CIRCUITSTATE/PBSEQ-D2/Export/R0.1/[1] 12-05-2024/PCB/PBSEQ-D2-R0.1-F_Paste.pdf

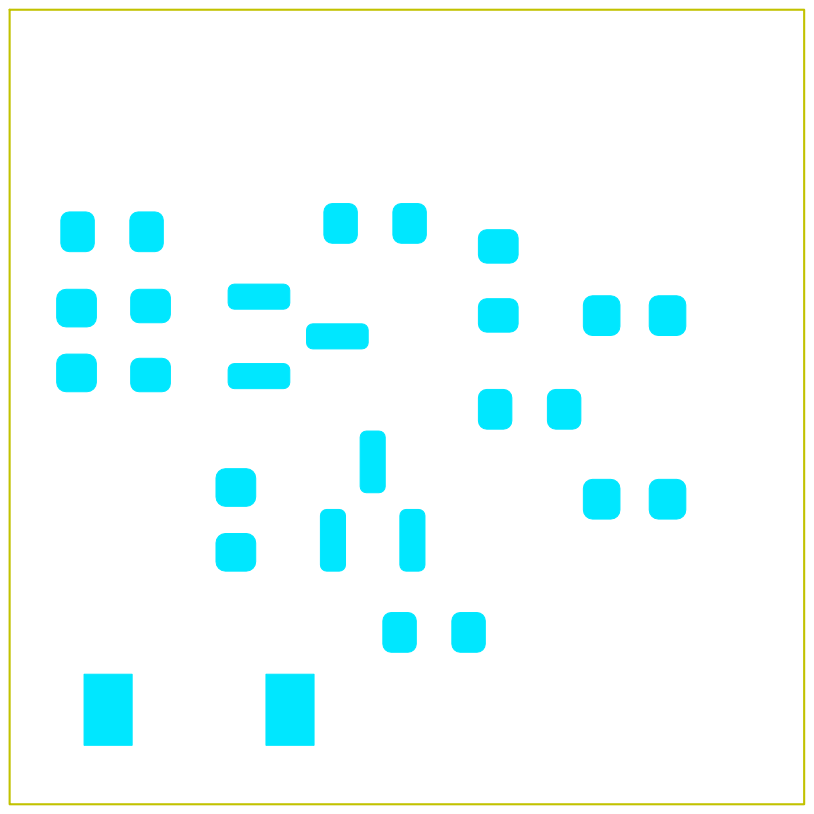
[picture p13: page 1]
