CIRCUITSTATE/PBSEQ-D2/Export/R0.1/[1] 12-05-2024/PCB/PBSEQ-D2-R0.1-F_Silkscreen.pdf

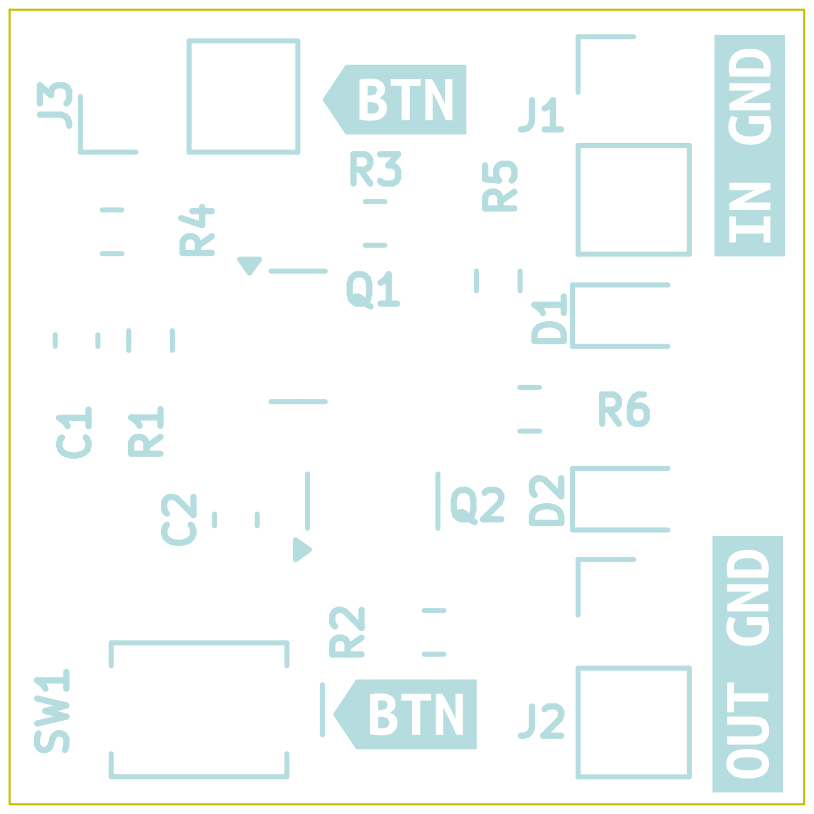
[picture p14: page 1]
