CIRCUITSTATE/PBSEQ-D2/Export/R0.1/[1] 12-05-2024/PCB/PBSEQ-D2-R0.1-User_Drawings.pdf

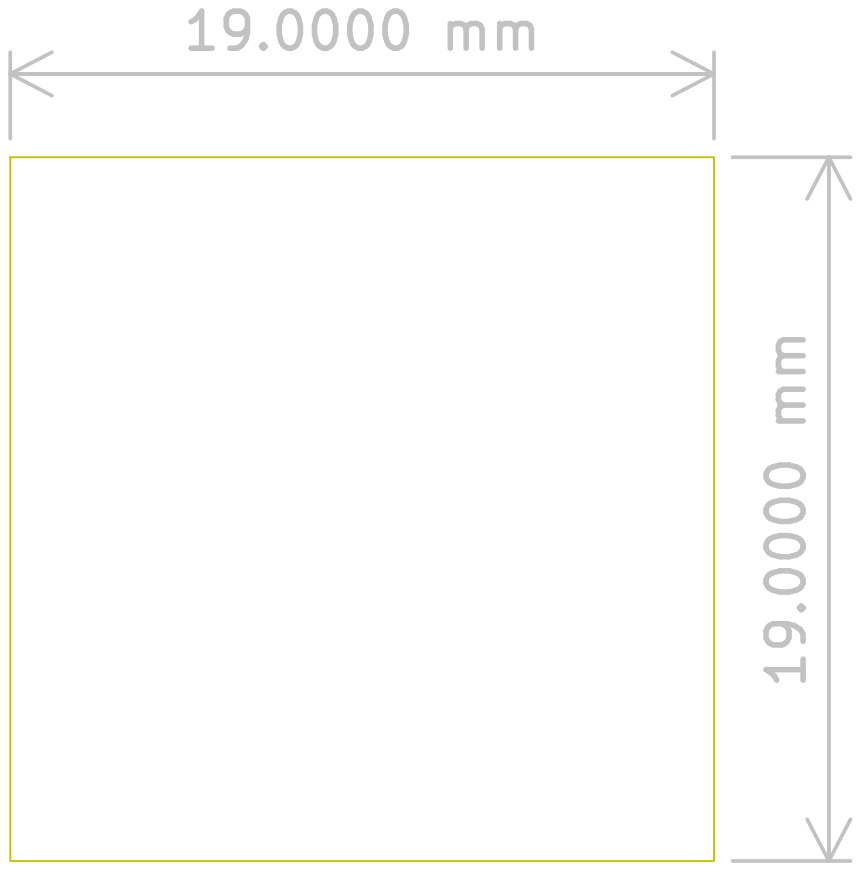
[picture p15: page 1]
