CIRCUITSTATE/PBSEQ-D2/Export/R0.1/[1] 12-05-2024/SCH/PBSEQ-D2-R0.1-SCH-12052024-1.pdf

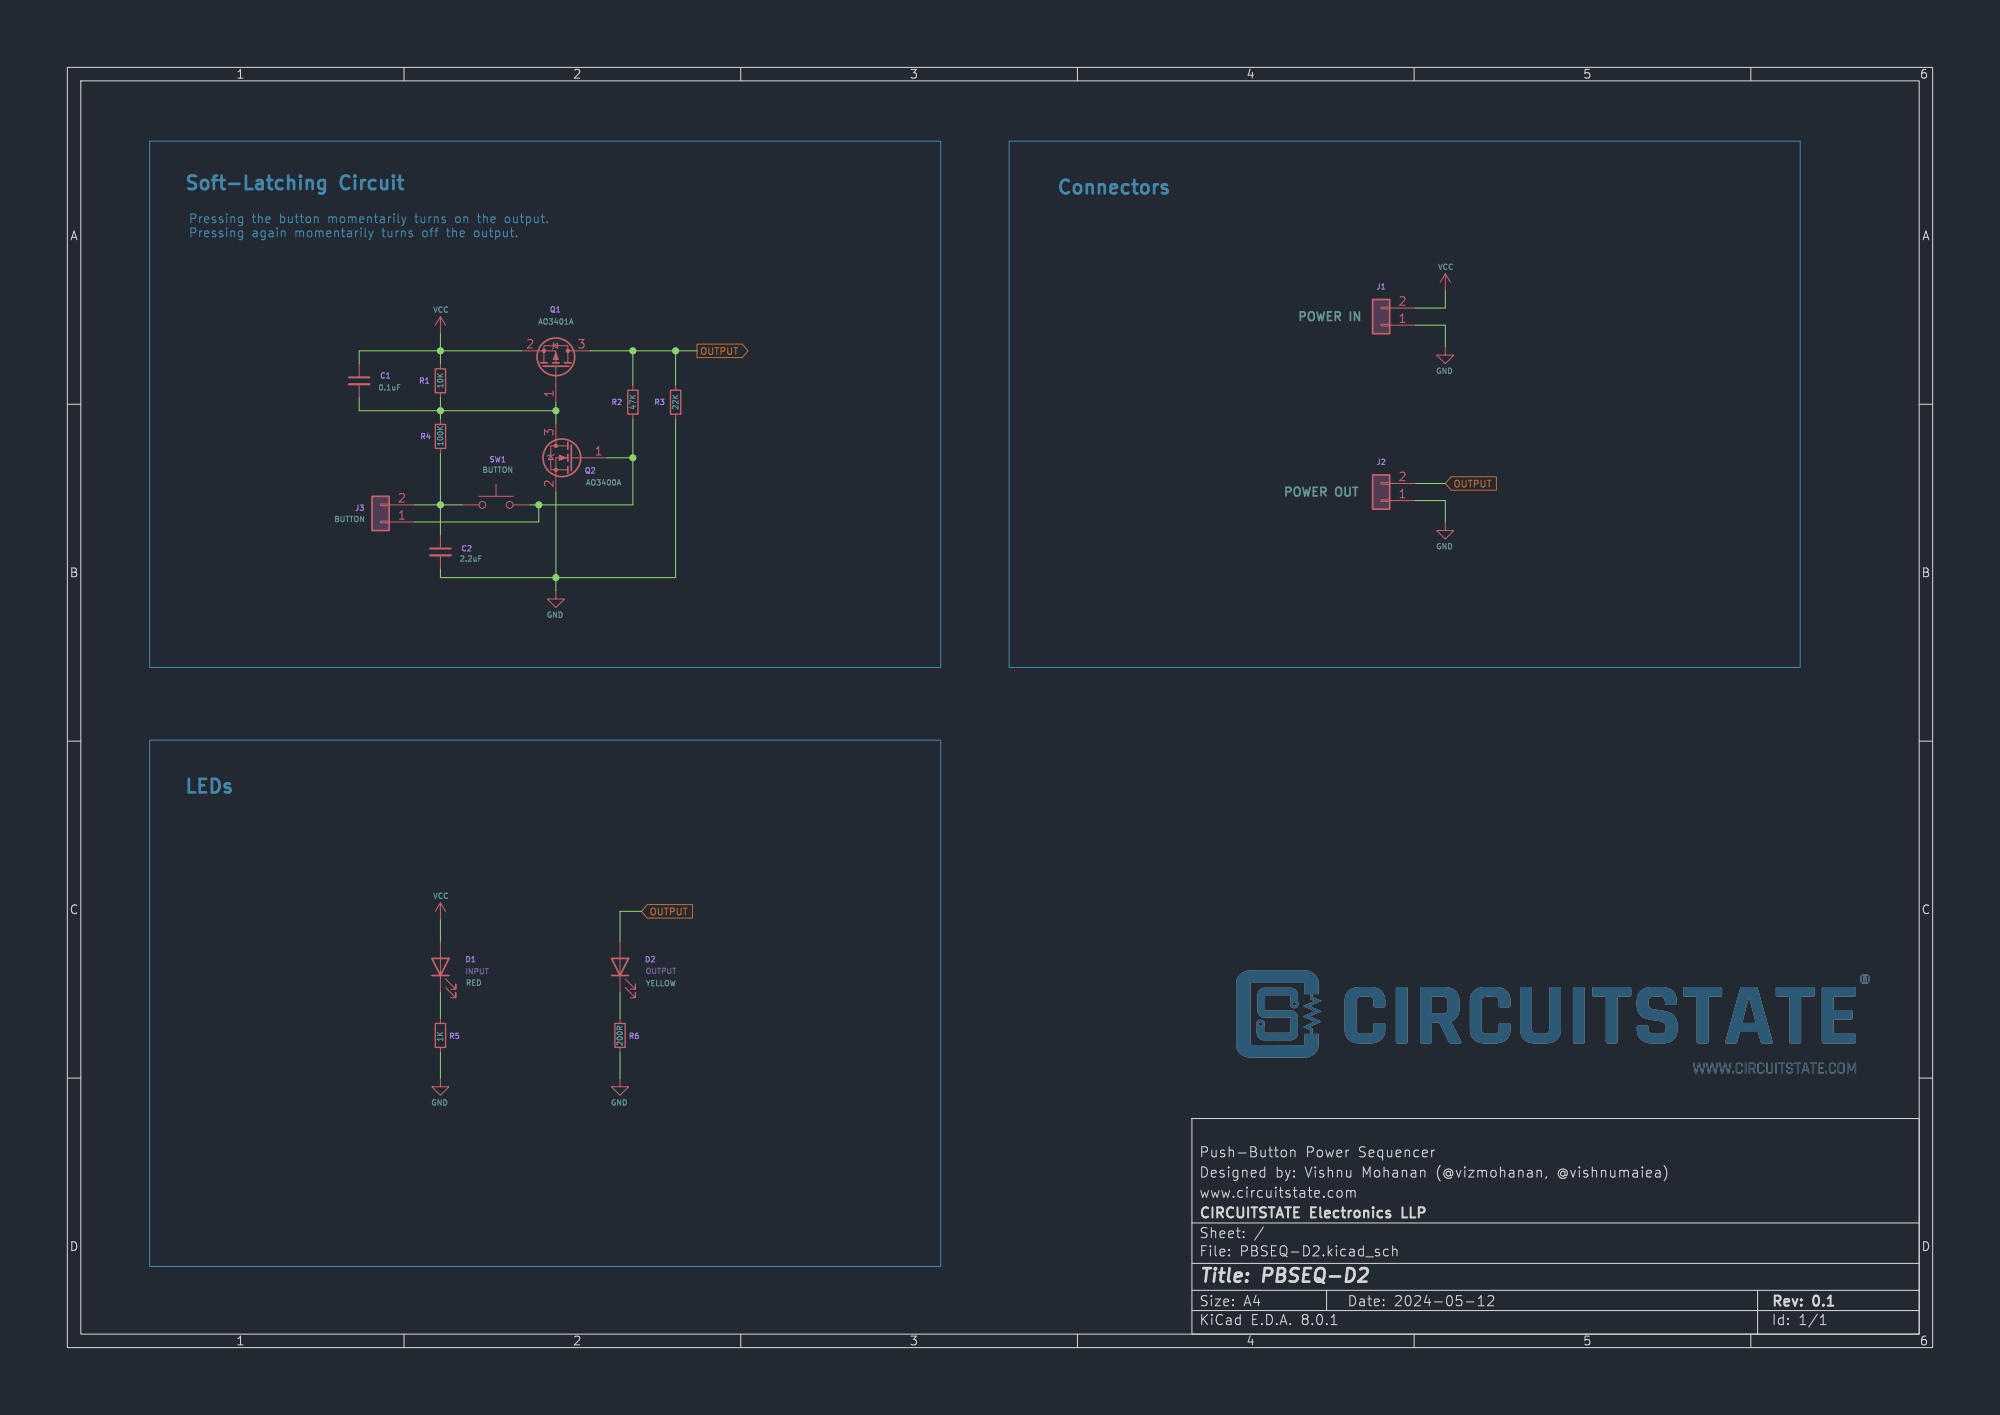
[picture p16: page 1]
